CtrlAltJon/PeterThePowerMeter/Images/enclosure/peter-box-01.jpg

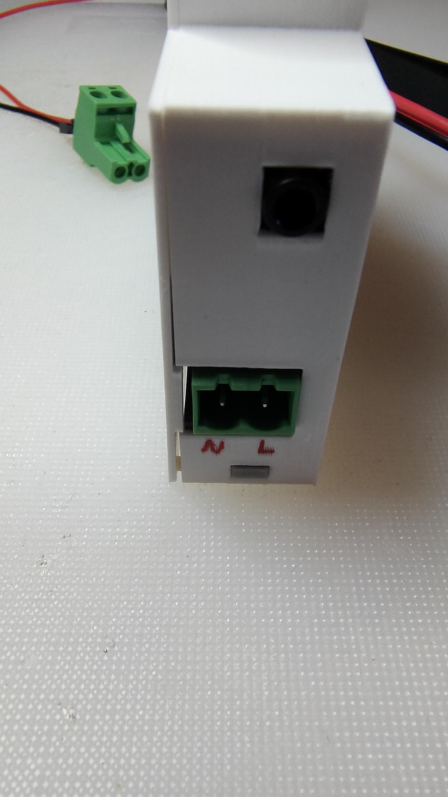
Images/enclosure/peter-box-01.jpg
