CtrlAltJon/PeterThePowerMeter/Images/enclosure/peter-box-02.jpg

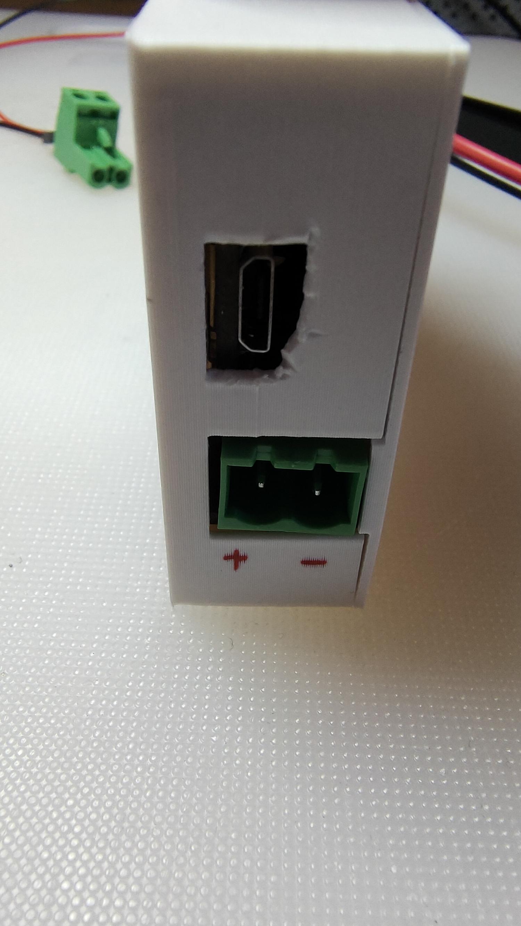
Images/enclosure/peter-box-02.jpg
