CtrlAltJon/PeterThePowerMeter/Images/firmware/peter-fw-01.jpg

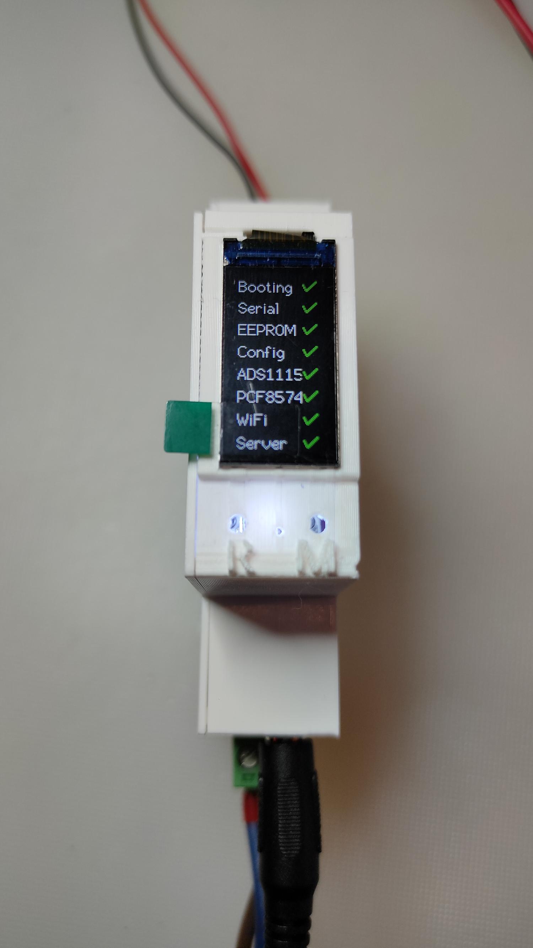
Images/firmware/peter-fw-01.jpg
