CtrlAltJon/PeterThePowerMeter/Images/firmware/peter-fw-03.jpg

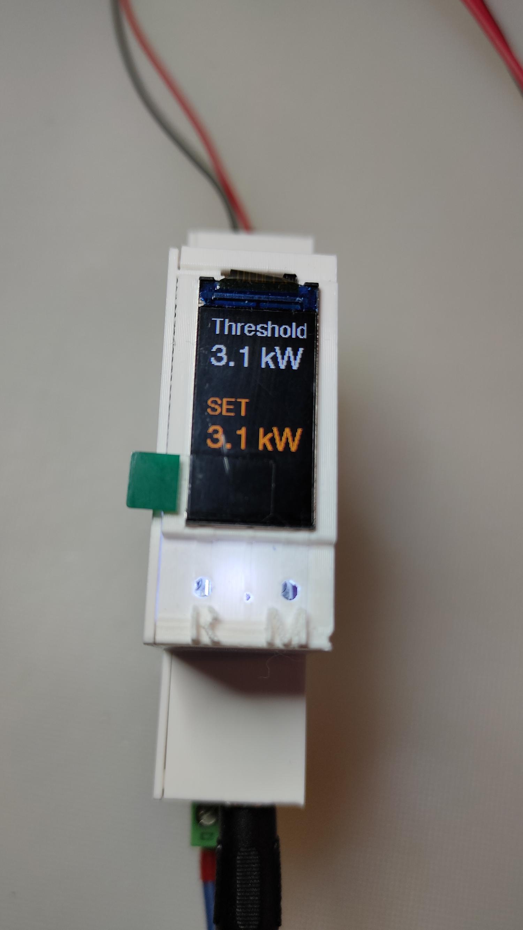
Images/firmware/peter-fw-03.jpg
