CtrlAltJon/PeterThePowerMeter/Images/firmware/peter-fw-04.jpg

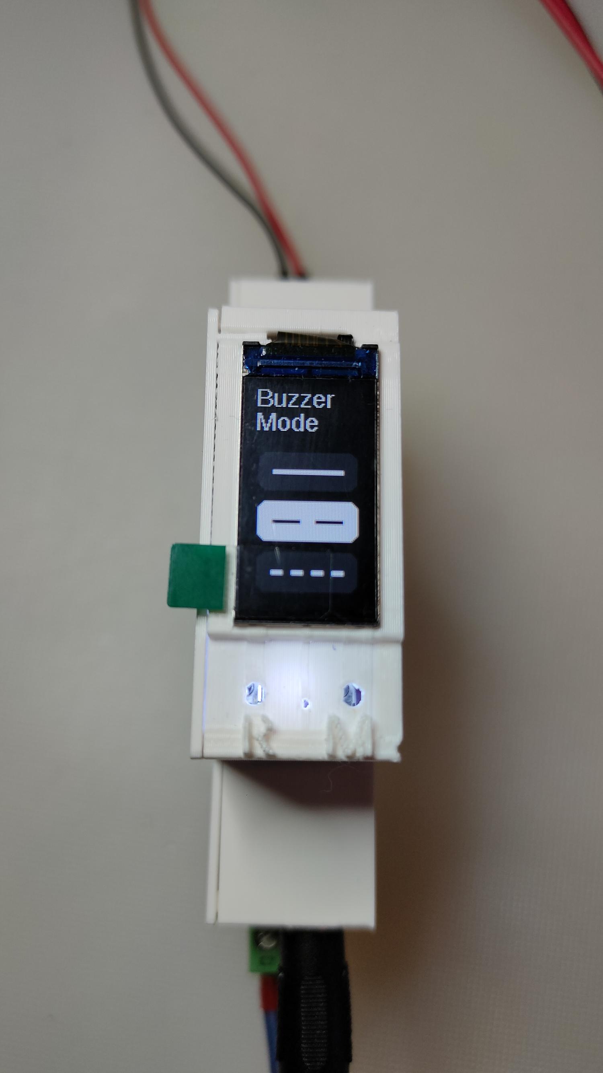
Images/firmware/peter-fw-04.jpg
