CtrlAltJon/PeterThePowerMeter/Images/firmware/peter-fw-06.jpg

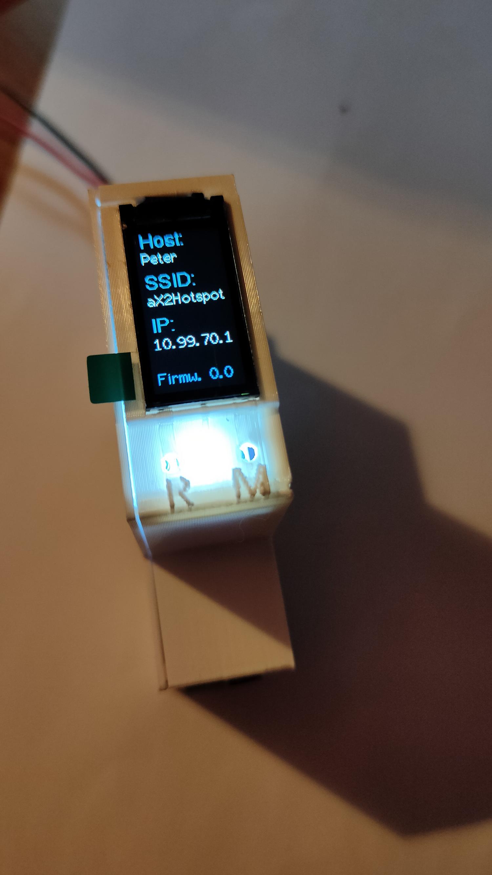
Images/firmware/peter-fw-06.jpg
