CtrlAltJon/PeterThePowerMeter/Images/firmware/peter-fw-07.jpg

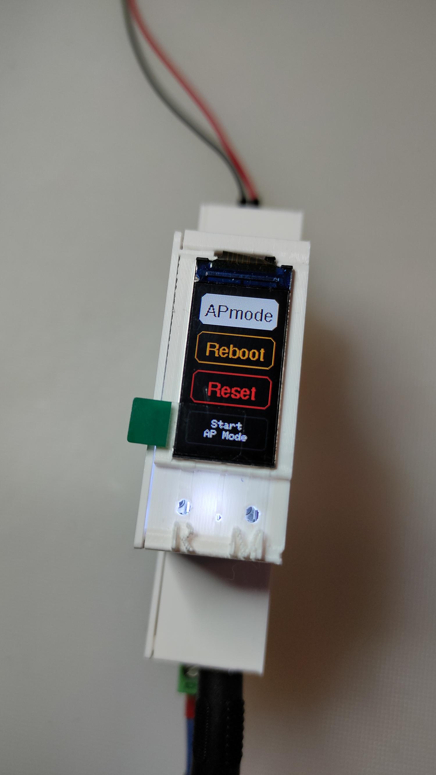
Images/firmware/peter-fw-07.jpg
