CtrlAltJon/PeterThePowerMeter/Images/firmware/peter-fw-09.jpg

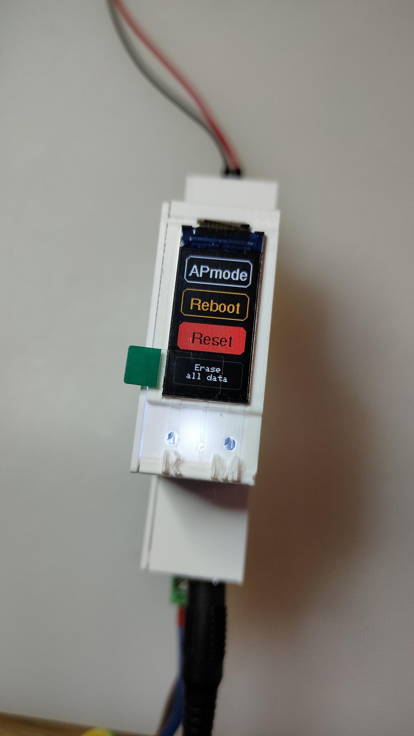
Images/firmware/peter-fw-09.jpg
