CtrlAltJon/PeterThePowerMeter/Images/hardware/peter-hw-03.jpg

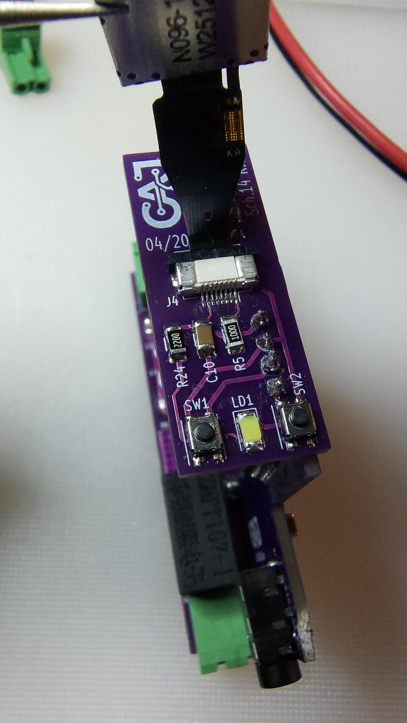
Images/hardware/peter-hw-03.jpg
