CtrlAltJon/PeterThePowerMeter/Images/hardware/peter-hw-04.jpg

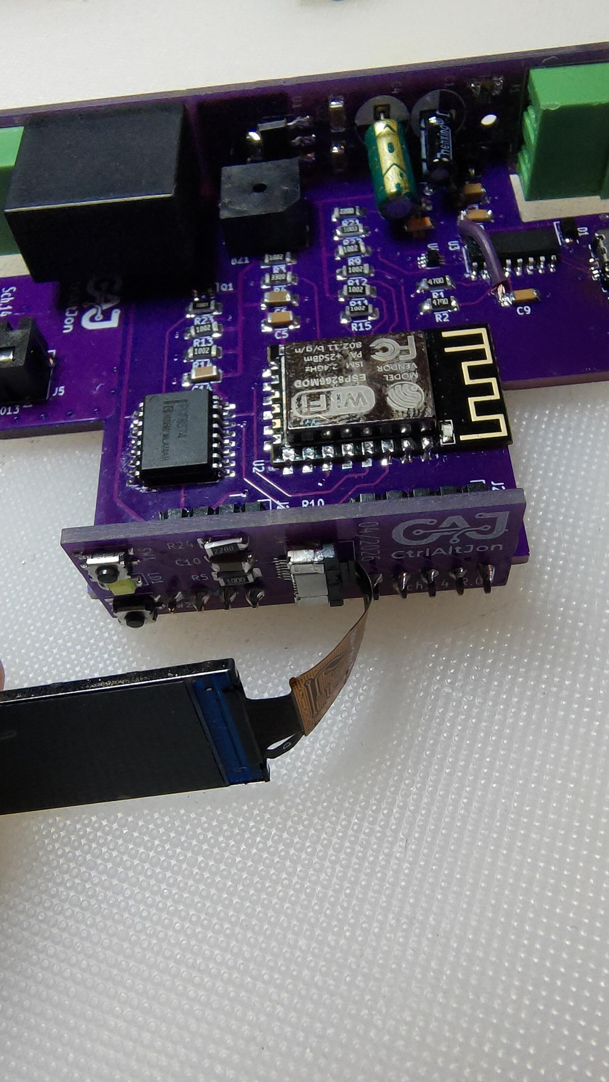
Images/hardware/peter-hw-04.jpg
