CtrlAltJon/PeterThePowerMeter/Images/hardware/peter-hw-07.jpg

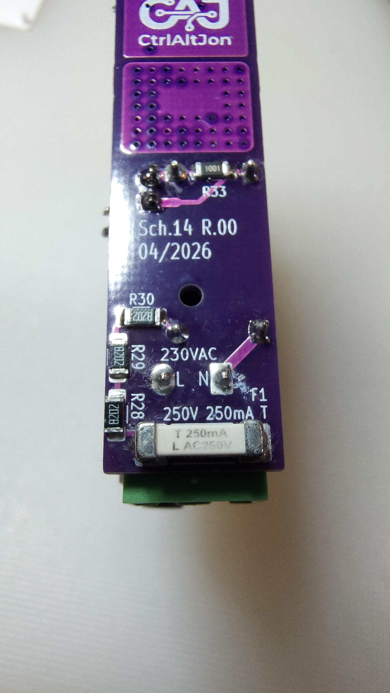
Images/hardware/peter-hw-07.jpg
