CtrlAltJon/PeterThePowerMeter/Images/hardware/peter-hw-09.jpg

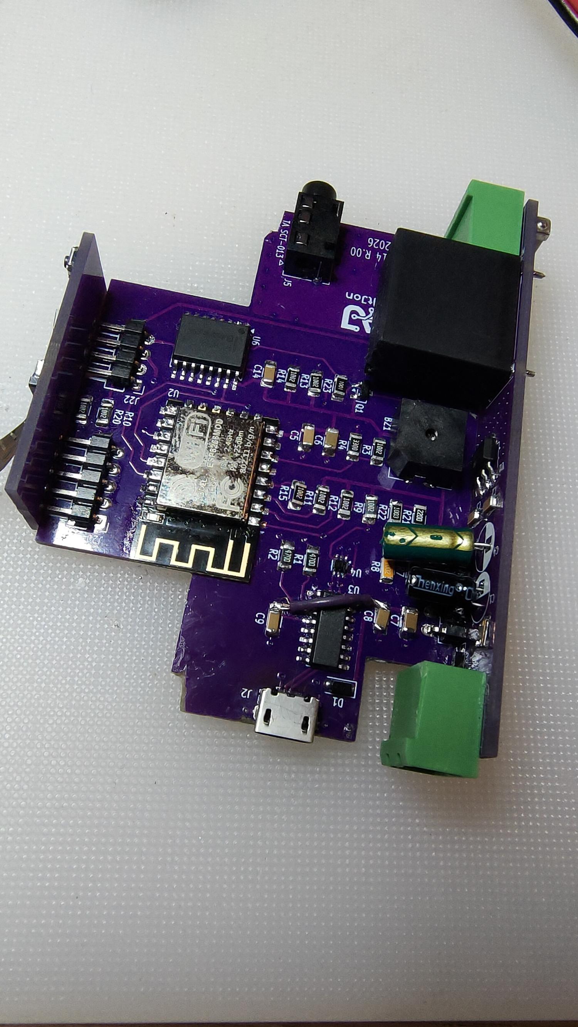
Images/hardware/peter-hw-09.jpg
