CtrlAltJon/PeterThePowerMeter/Images/web-server/peter-web-01.jpg

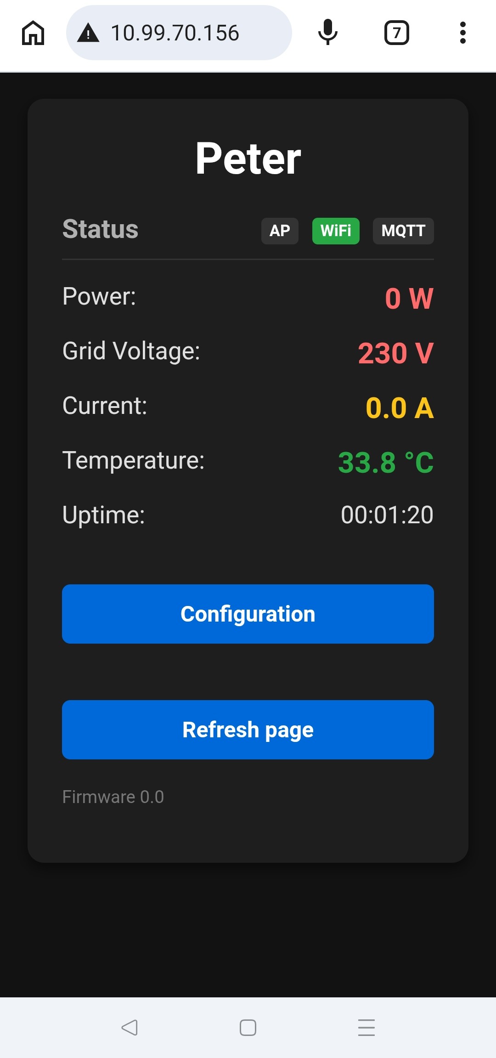
Images/web-server/peter-web-01.jpg
