CtrlAltJon/PeterThePowerMeter/Images/web-server/peter-web-02.jpg

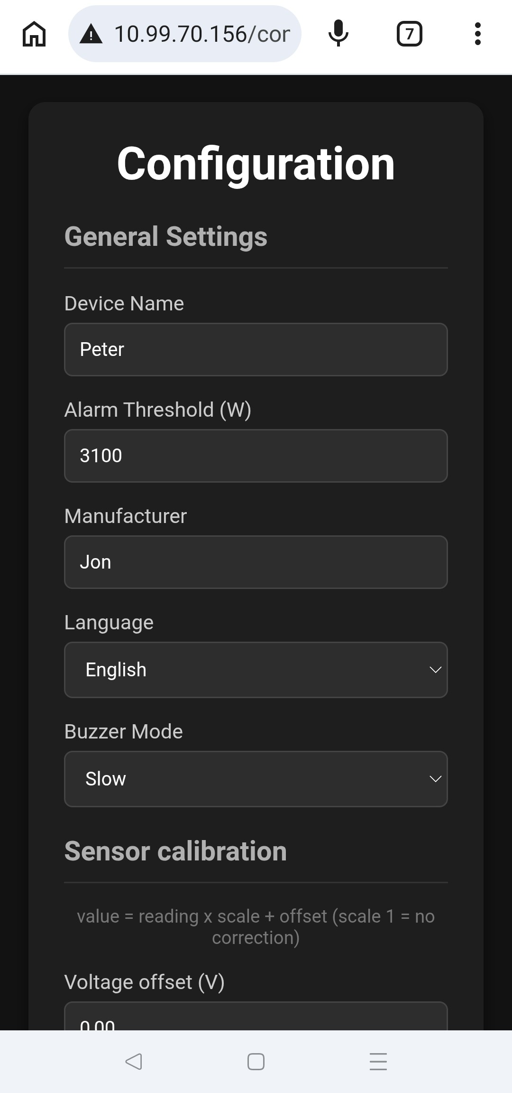
Images/web-server/peter-web-02.jpg
