CtrlAltJon/PeterThePowerMeter/Images/web-server/peter-web-03.jpg

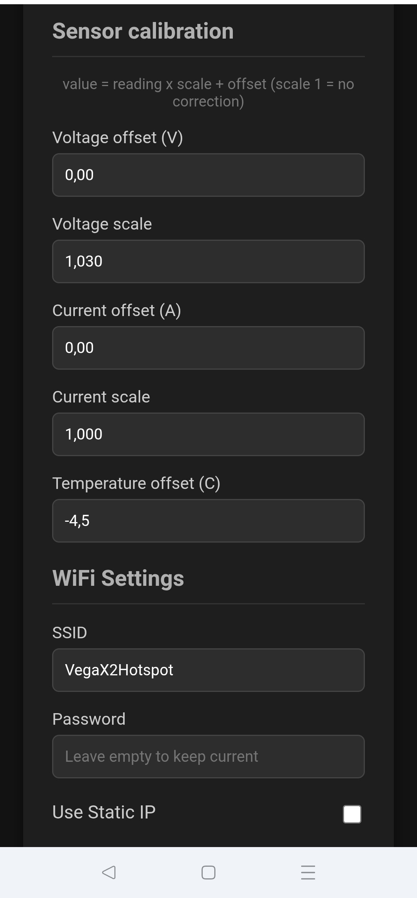
Images/web-server/peter-web-03.jpg
