CtrlAltJon/PeterThePowerMeter/Images/web-server/peter-web-04.jpg

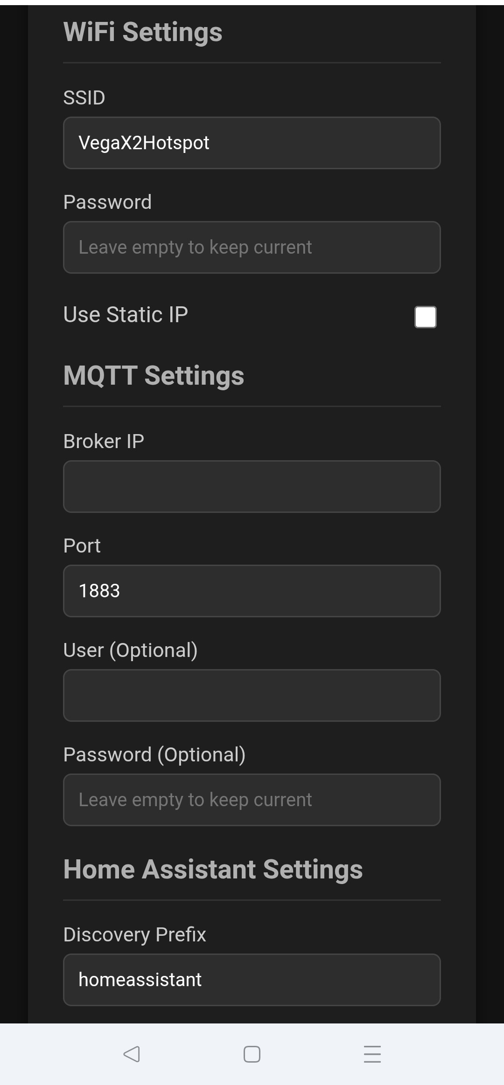
Images/web-server/peter-web-04.jpg
