CtrlAltJon/PeterThePowerMeter/Images/web-server/peter-web-05.jpg

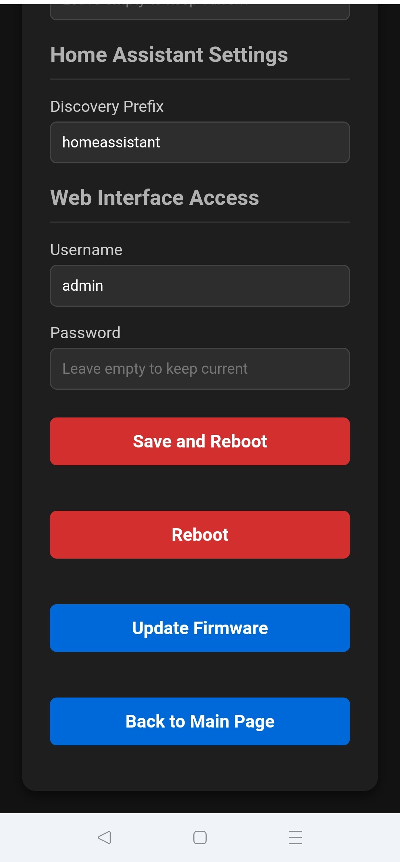
Images/web-server/peter-web-05.jpg
