CtrlAltJon/PeterThePowerMeter/Images/guide-docs/Guide_Assembly-Bottom.png

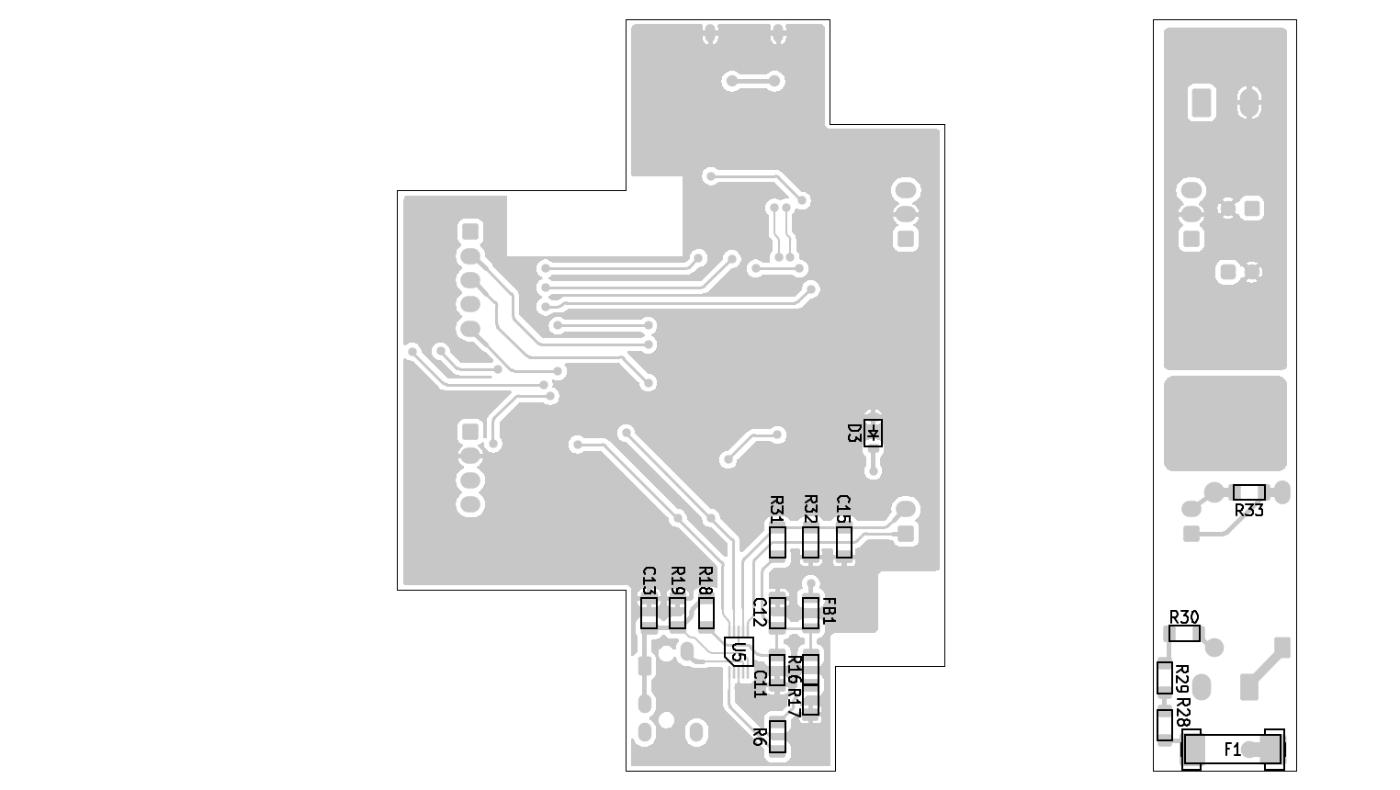
Images/guide-docs/Guide_Assembly-Bottom.png
