CtrlAltJon/PeterThePowerMeter/Images/guide-docs/Guide_Assembly-Top.png

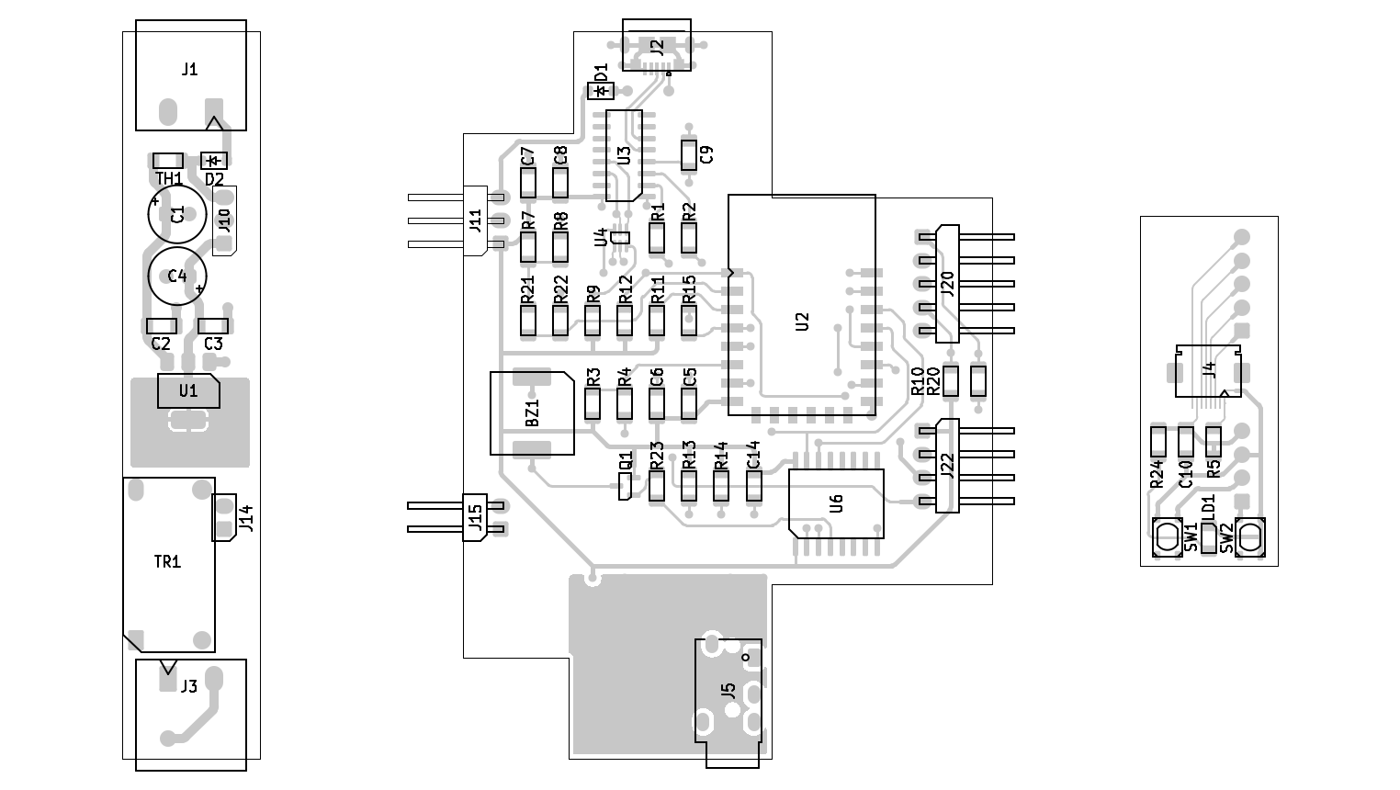
Images/guide-docs/Guide_Assembly-Top.png
