CtrlAltJon/PeterThePowerMeter/Images/guide-docs/Guide_J3.png

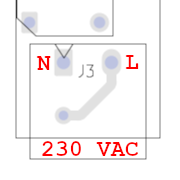
Images/guide-docs/Guide_J3.png
