CtrlAltJon/PeterThePowerMeter/Images/measures/peter-consumption-01.jpg

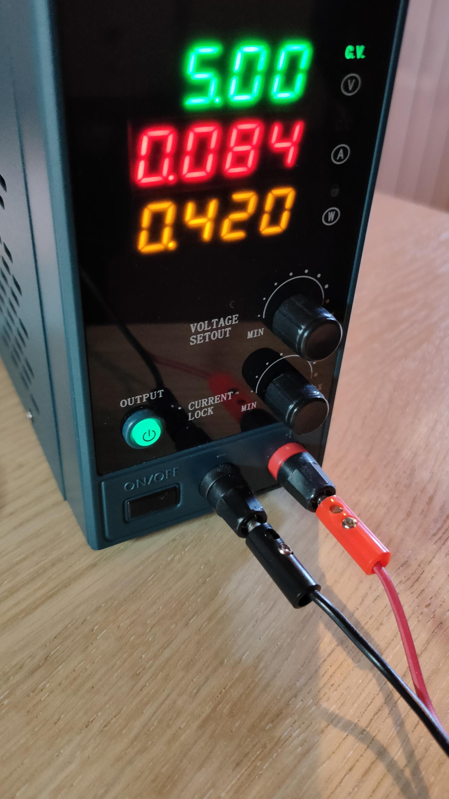
Images/measures/peter-consumption-01.jpg
